MartinHepperle/HP-ReproParts/HP 9000/HP-9836-Handle.stl

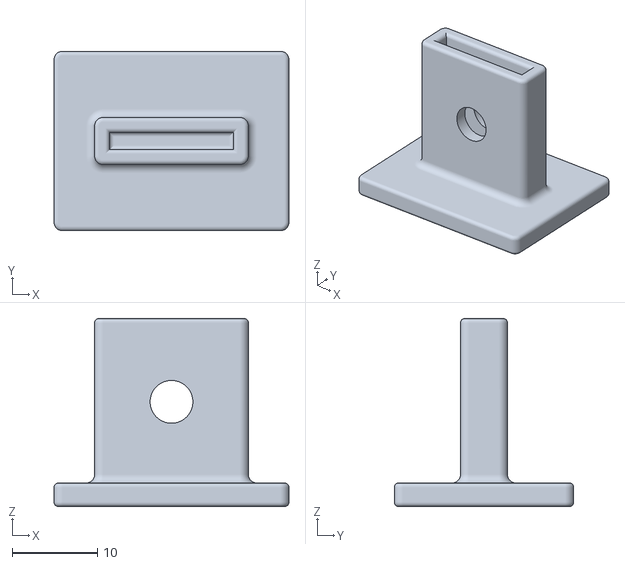
[picture p20: CAD file, 2022-06-20]
HP 9000/HP-9836-Handle.stl
27.5 x 21.0 x 22.0
