MartinHepperle/HP-ReproParts/HP3456A/3456A-FrontBracket.stl

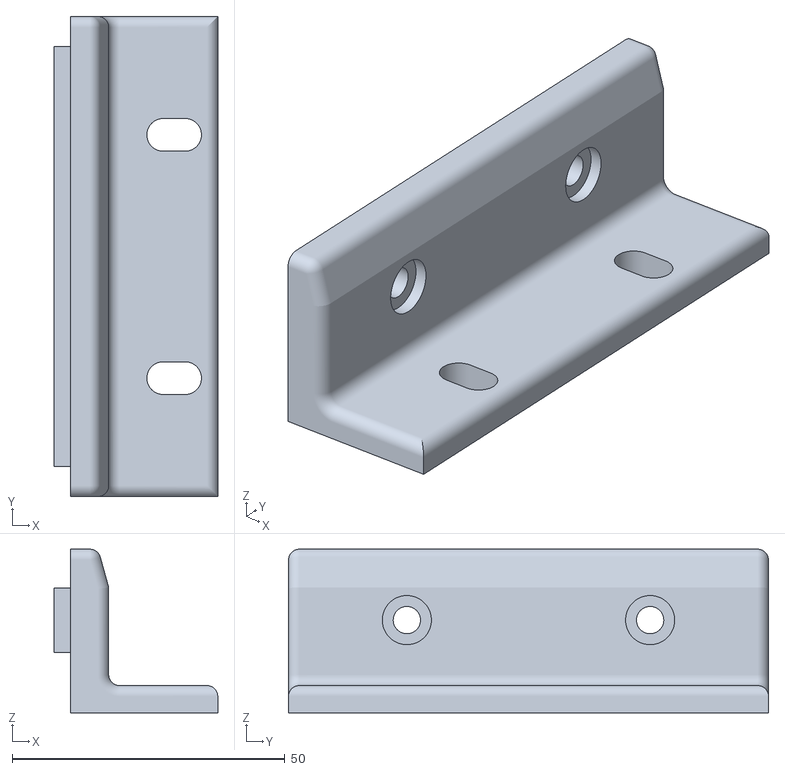
[picture p21: CAD file, 2020-10-23]
HP3456A/3456A-FrontBracket.stl
30.0 x 88.0 x 30.0
