MartinHepperle/HP-ReproParts/HP9825/9825-case-bot.stl

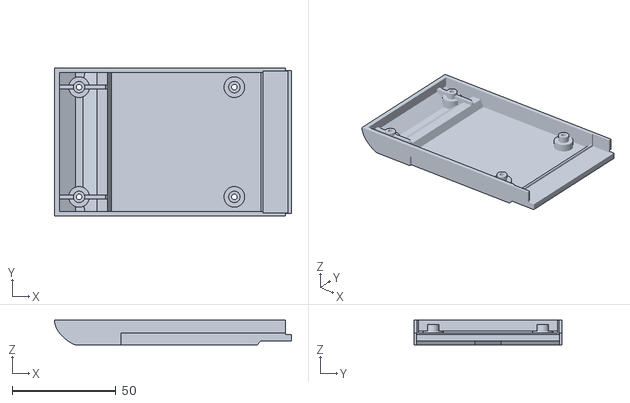
[picture p22: CAD file, 2020-07-03]
HP9825/9825-case-bot.stl
114.5 x 71.5 x 11.9
