MartinHepperle/HP-ReproParts/HP9825/9825-case-top.stl

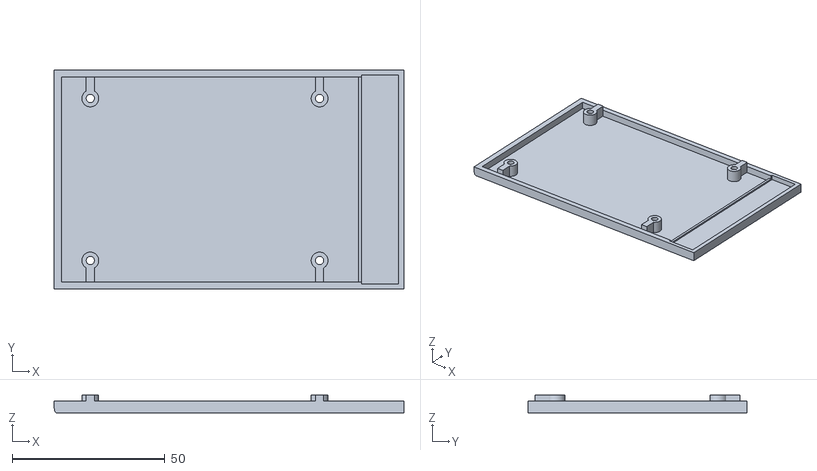
[picture p23: CAD file, 2020-07-03]
HP9825/9825-case-top.stl
114.5 x 71.5 x 5.80
